MOSH-Insa-Toulouse/2021-2022-Projet-Capteur-Pommier-Alvarez/APK/code_graphique.png

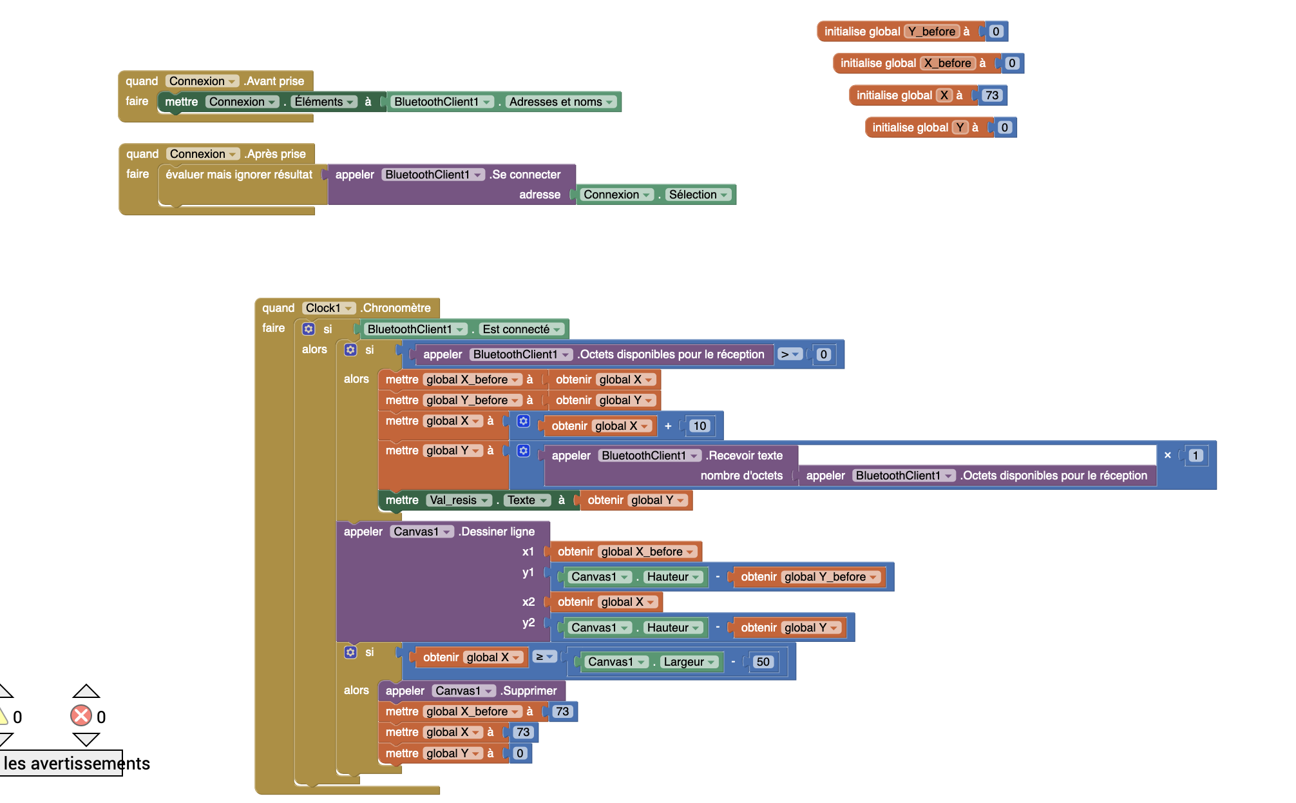
APK/code_graphique.png
