MOSH-Insa-Toulouse/2021-2022-Projet-Capteur-Pommier-Alvarez/Banc_de_test/banc_de_test3.JPG

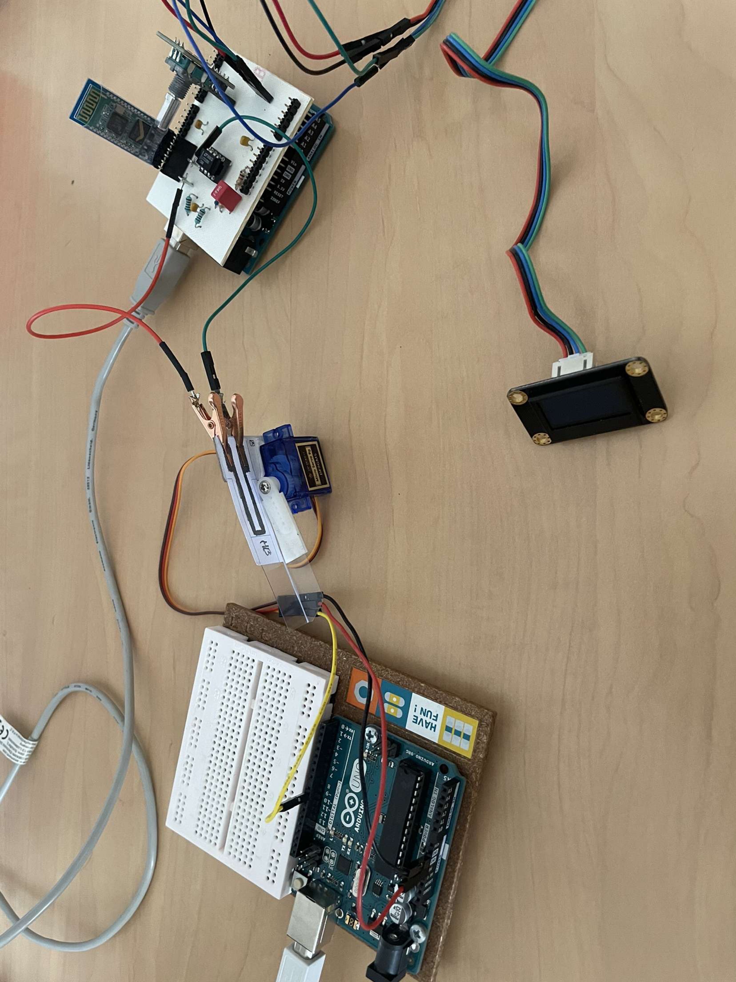
Banc_de_test/banc_de_test3.JPG
